JordanAceto/micro-pico/images/angle_2.JPG

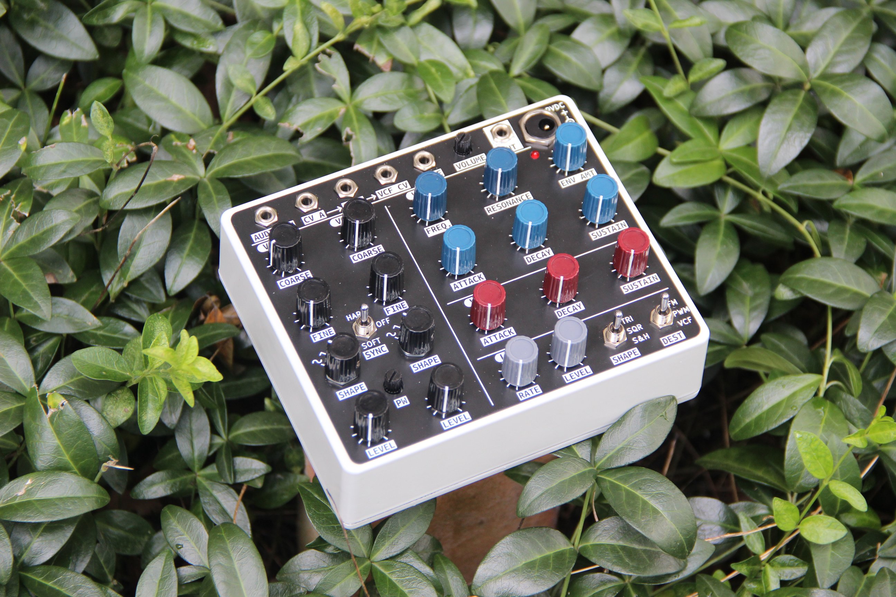
images/angle_2.JPG
