JordanAceto/micro-pico/images/front.JPG

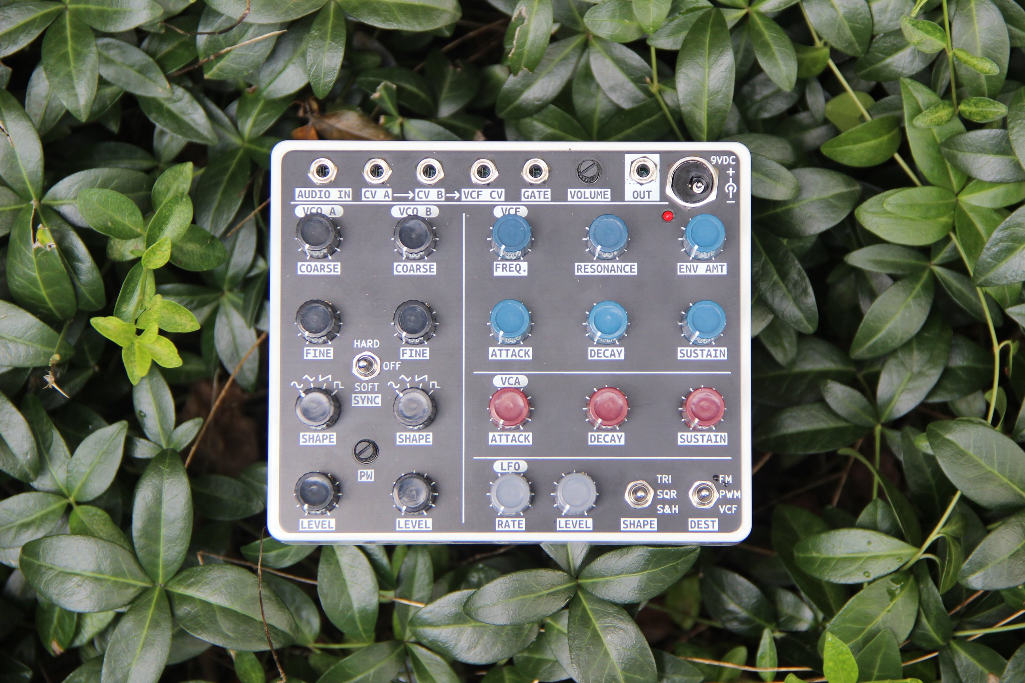
images/front.JPG
