JordanAceto/micro-pico/main_pcb/docs/2D/micro_pico-top.jpg

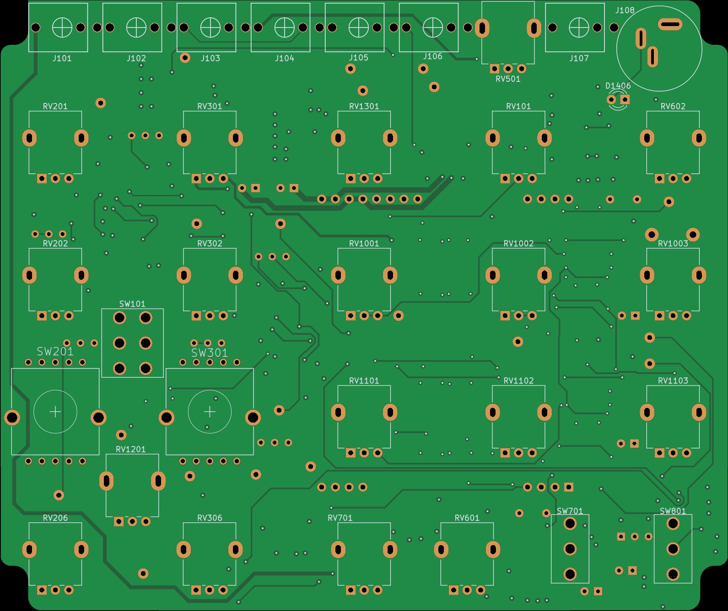
main_pcb/docs/2D/micro_pico-top.jpg
