JordanAceto/micro-pico/main_pcb/docs/html_nav/images/cat_pcb_bottom_jpg_micro_pico-bottom.png

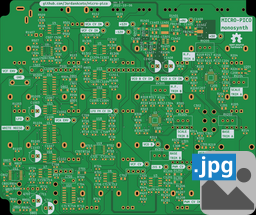
main_pcb/docs/html_nav/images/cat_pcb_bottom_jpg_micro_pico-bottom.png
