JordanAceto/micro-pico/main_pcb/docs/html_nav/images/cat_PCB_micro_pico-F_Cu.png

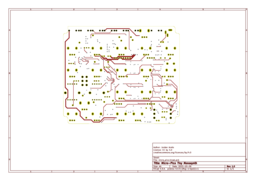
main_pcb/docs/html_nav/images/cat_PCB_micro_pico-F_Cu.png
