JordanAceto/micro-pico/main_pcb/docs/html_nav/images/cat_pcb_top_jpg_micro_pico-top.png

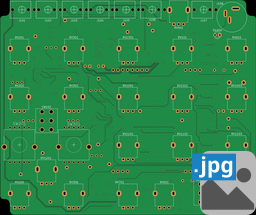
main_pcb/docs/html_nav/images/cat_pcb_top_jpg_micro_pico-top.png
