JordanAceto/micro-pico/main_pcb/docs/html_nav/images/cat_pdf_layers_micro_pico-B_Paste.png

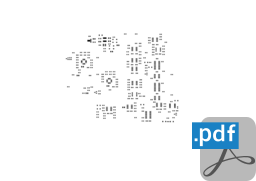
main_pcb/docs/html_nav/images/cat_pdf_layers_micro_pico-B_Paste.png
