JordanAceto/micro-pico/main_pcb/docs/html_nav/images/cat_pdf_layers_micro_pico-F_Courtyard.png

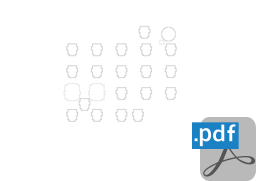
main_pcb/docs/html_nav/images/cat_pdf_layers_micro_pico-F_Courtyard.png
