JordanAceto/micro-pico/main_pcb/docs/html_nav/images/cat_pdf_sch_print_micro_pico-schematic.png

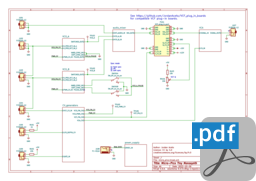
main_pcb/docs/html_nav/images/cat_pdf_sch_print_micro_pico-schematic.png
