JordanAceto/micro-pico/main_pcb/docs/2D/individual_layers/micro_pico-F_Cu.pdf

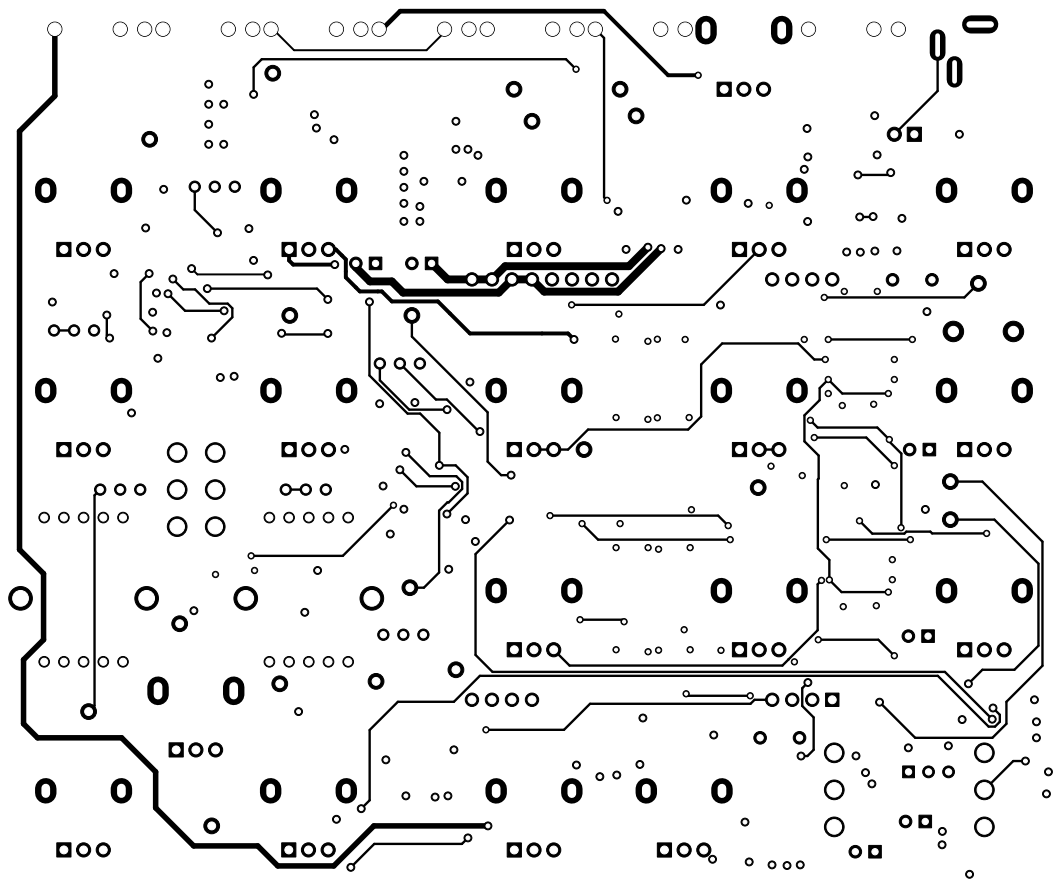
[picture p55: page 1]
