JordanAceto/micro-pico/main_pcb/docs/2D/individual_layers/micro_pico-F_Fab.pdf

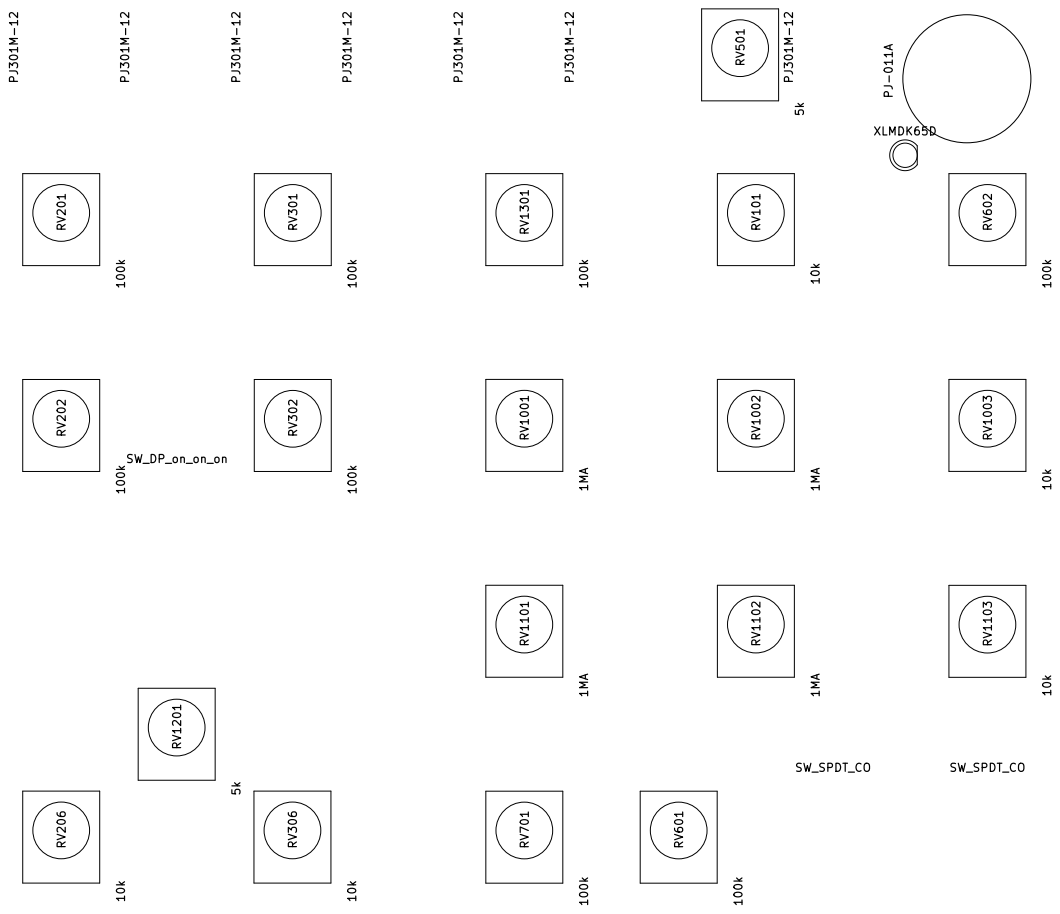
[picture p56: page 1]
