JordanAceto/micro-pico/main_pcb/docs/2D/individual_layers/micro_pico-F_Mask.pdf

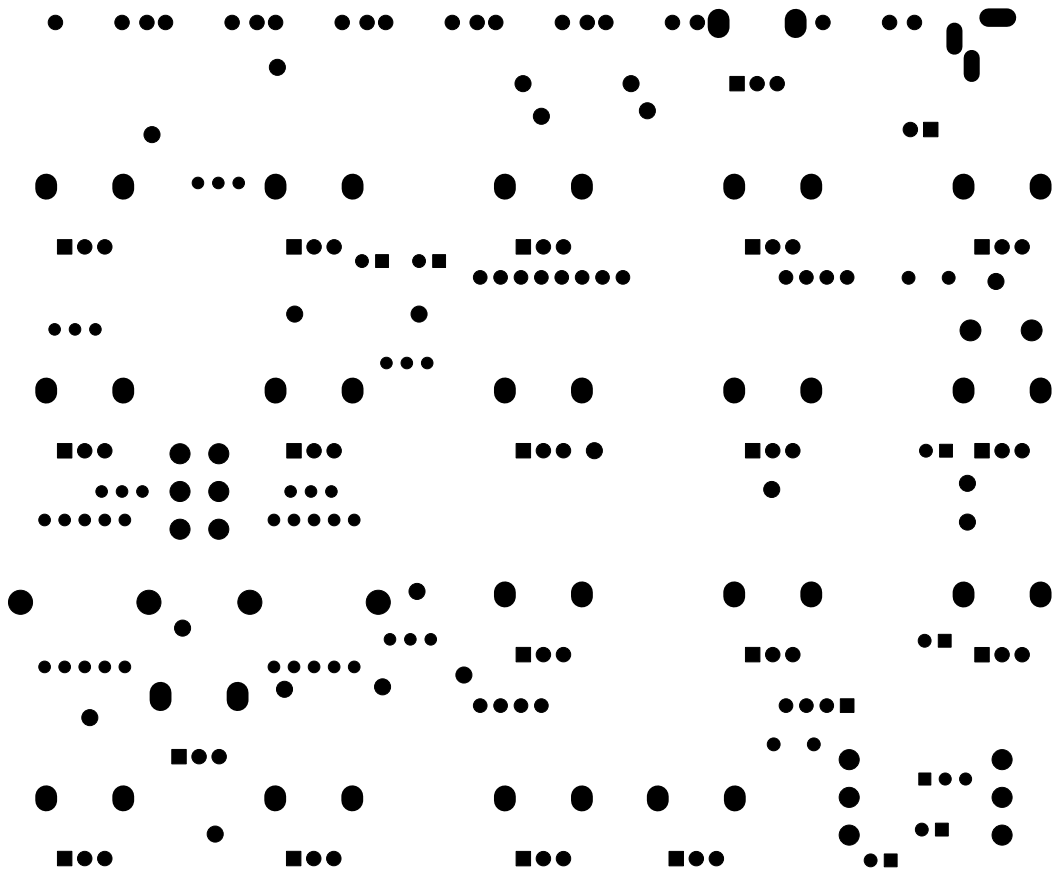
[picture p57: page 1]
