JordanAceto/micro-pico/main_pcb/docs/2D/individual_layers/micro_pico-F_Silkscreen.pdf

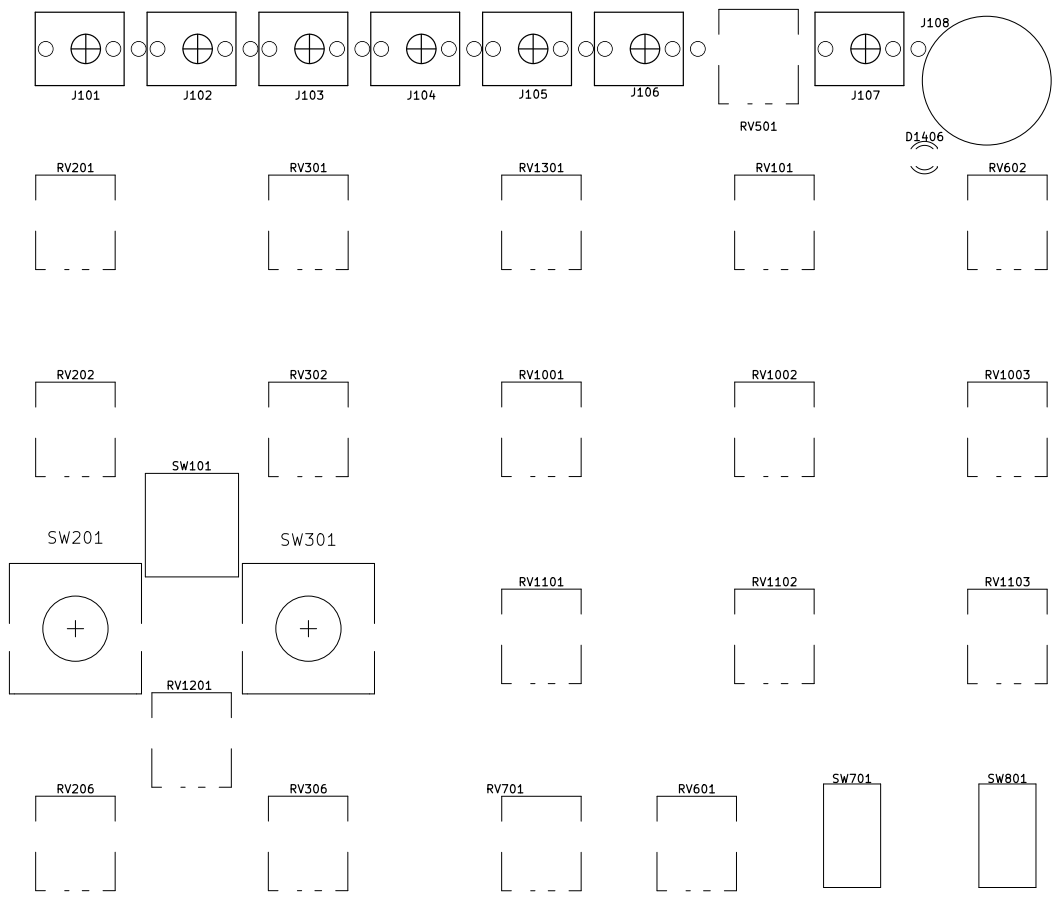
[picture p58: page 1]
