JordanAceto/micro-pico/main_pcb/docs/2D/individual_layers/micro_pico-In1_Cu.pdf

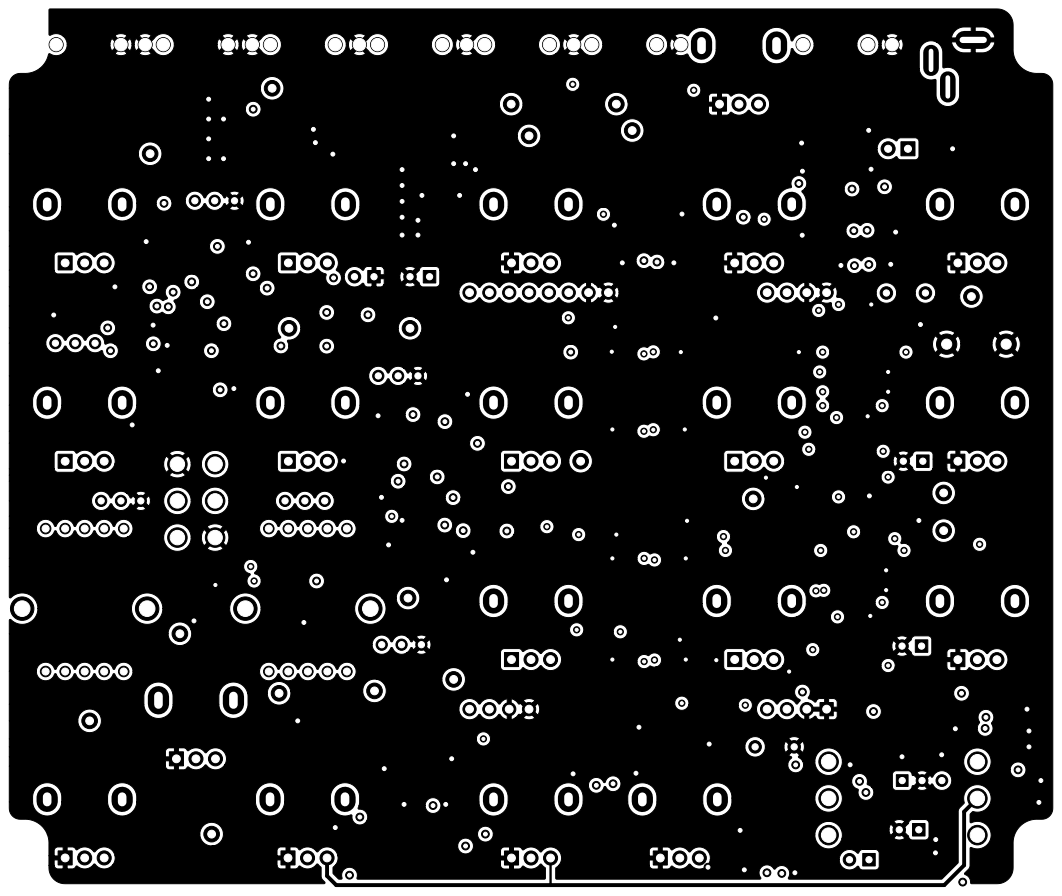
[picture p59: page 1]
