JordanAceto/micro-pico/main_pcb/docs/2D/individual_layers/micro_pico-In2_Cu.pdf

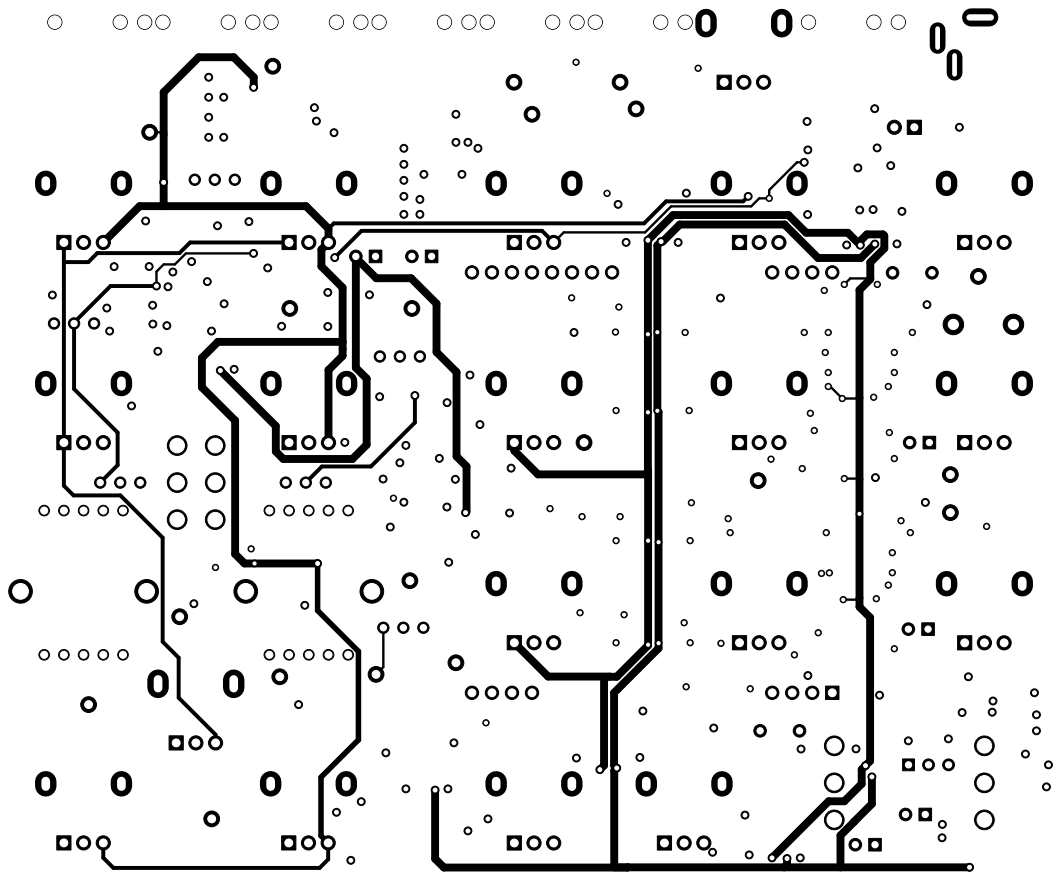
[picture p60: page 1]
